Dooncito/fundamentos-de-dise-o/Imagenes/Caja_Negra.png

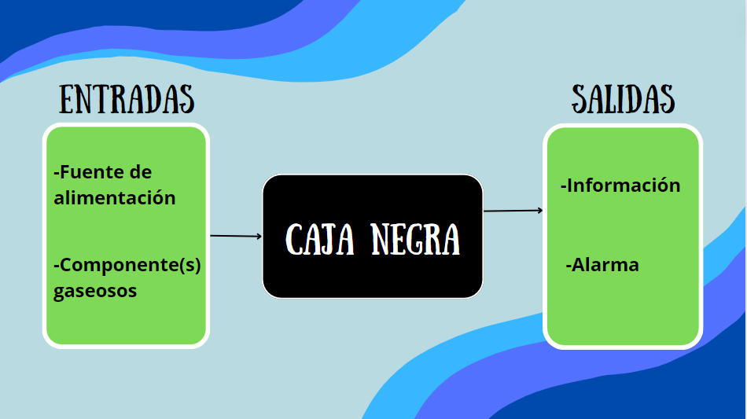
Imagenes/Caja_Negra.png
