Dooncito/fundamentos-de-dise-o/Imagenes/Esquema_de_Funciones.png

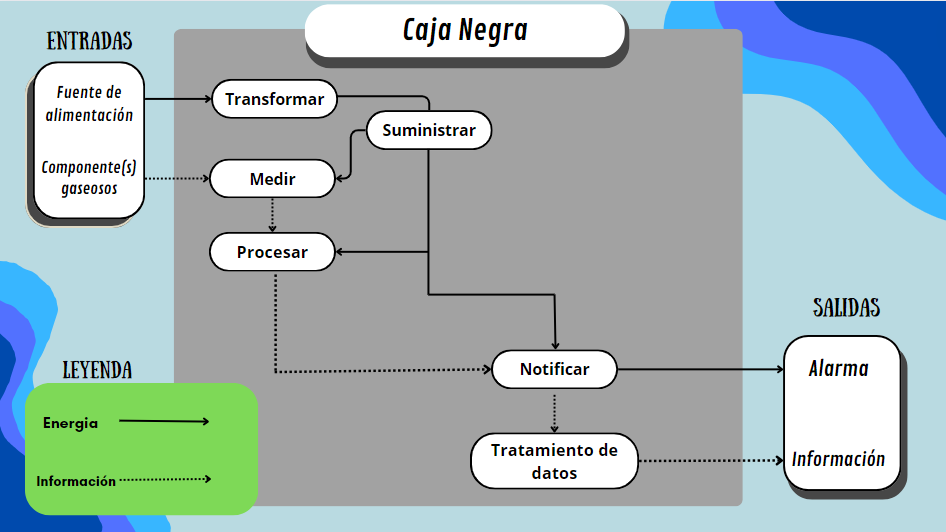
Imagenes/Esquema_de_Funciones.png
