Dooncito/fundamentos-de-dise-o/Imagenes/Funcionales.jpg

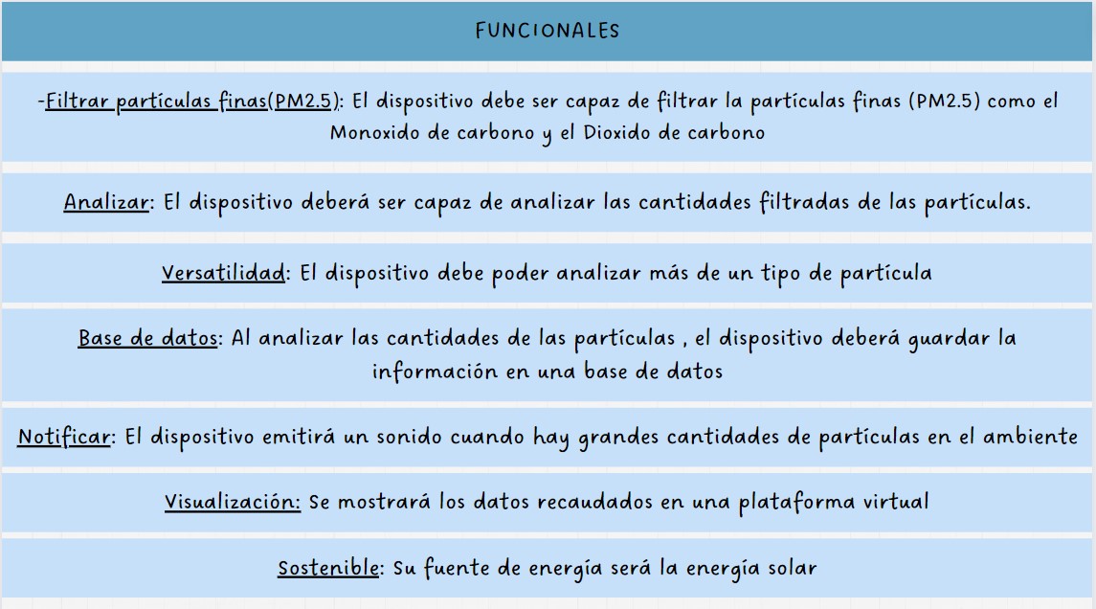
Imagenes/Funcionales.jpg
