Dooncito/fundamentos-de-dise-o/Imagenes/img entregable2/imgPro.jpg

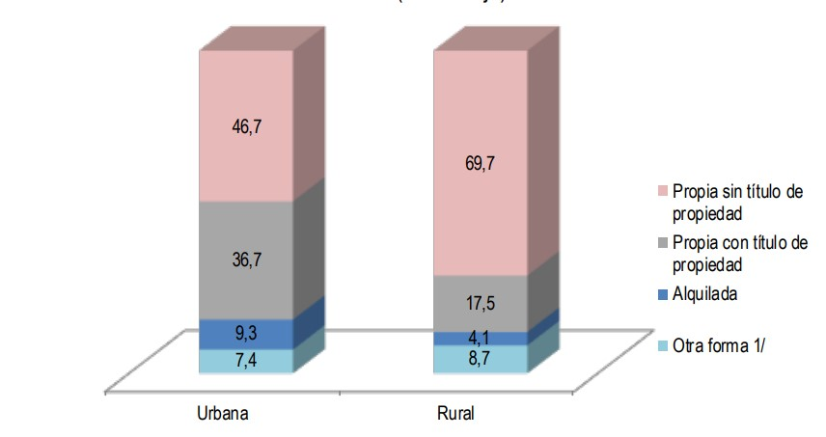
Imagenes/img entregable2/imgPro.jpg
