Dooncito/fundamentos-de-dise-o/Imagenes/img entregable2/Mapa de viaje.jpg

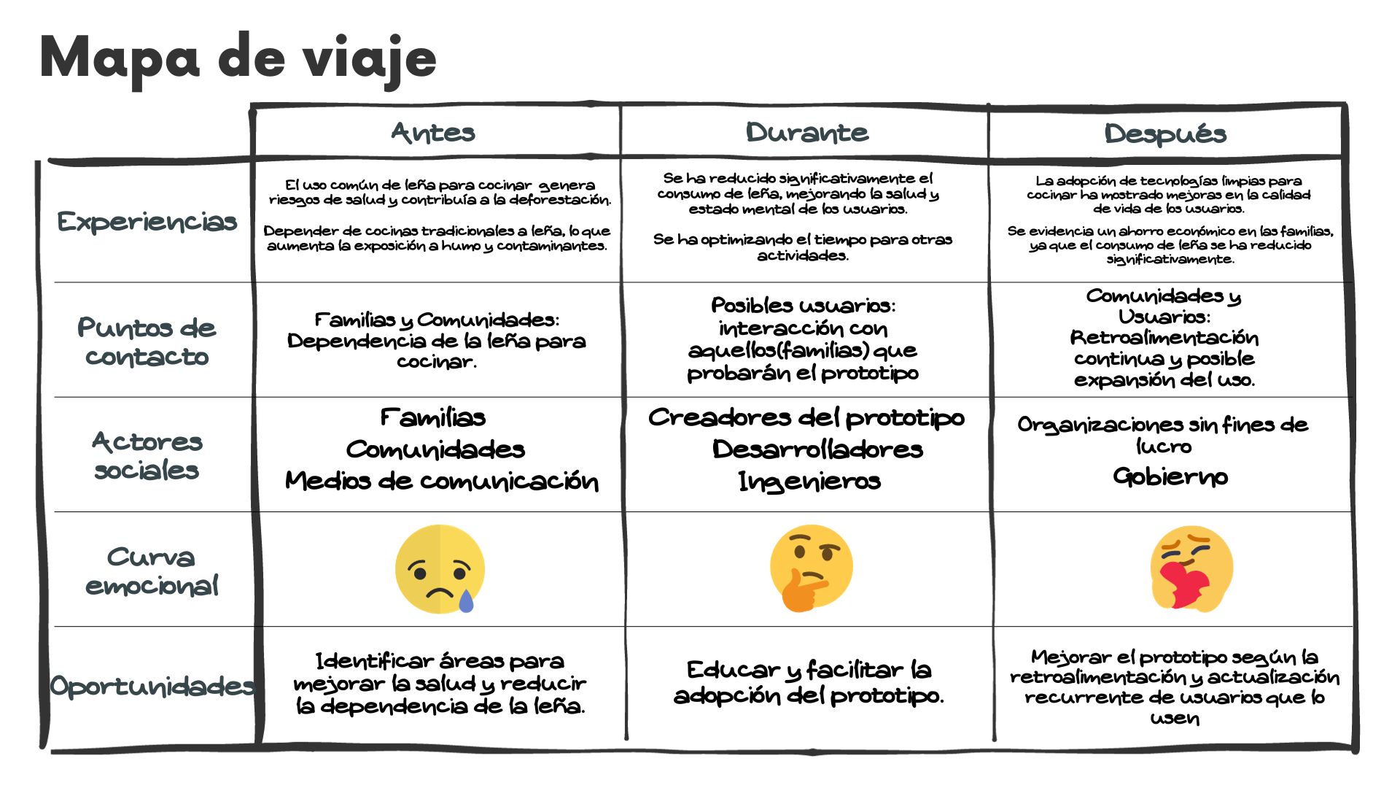
Imagenes/img entregable2/Mapa de viaje.jpg
