Dooncito/fundamentos-de-dise-o/Imagenes/img entregable2/Mapa empatía.jpg

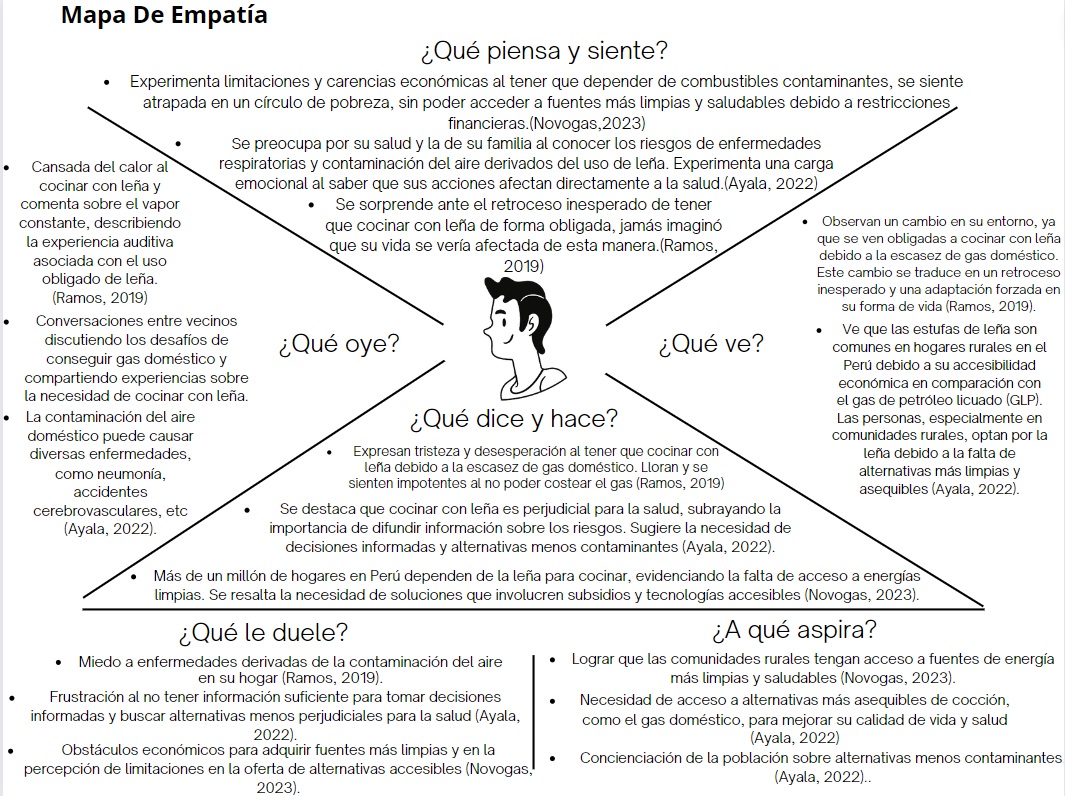
Imagenes/img entregable2/Mapa empatía.jpg
