Dooncito/fundamentos-de-dise-o/Imagenes/Img Monitoreo del aire.png

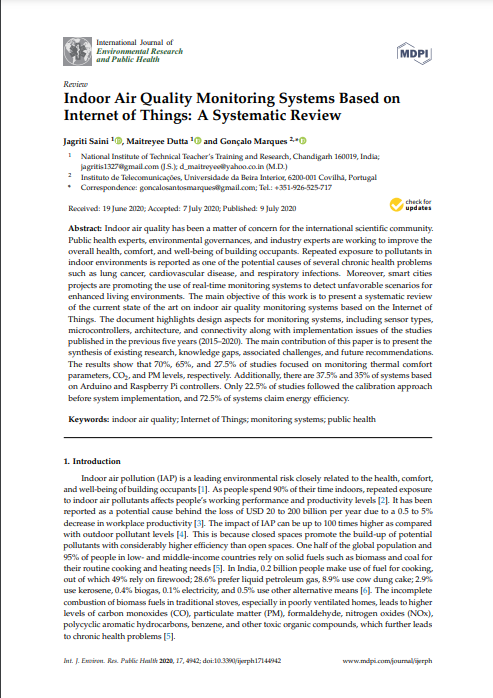
Imagenes/Img Monitoreo del aire.png
