Dooncito/fundamentos-de-dise-o/Imagenes/img_comercial_y_cienti/img anlásis de pm.jpeg

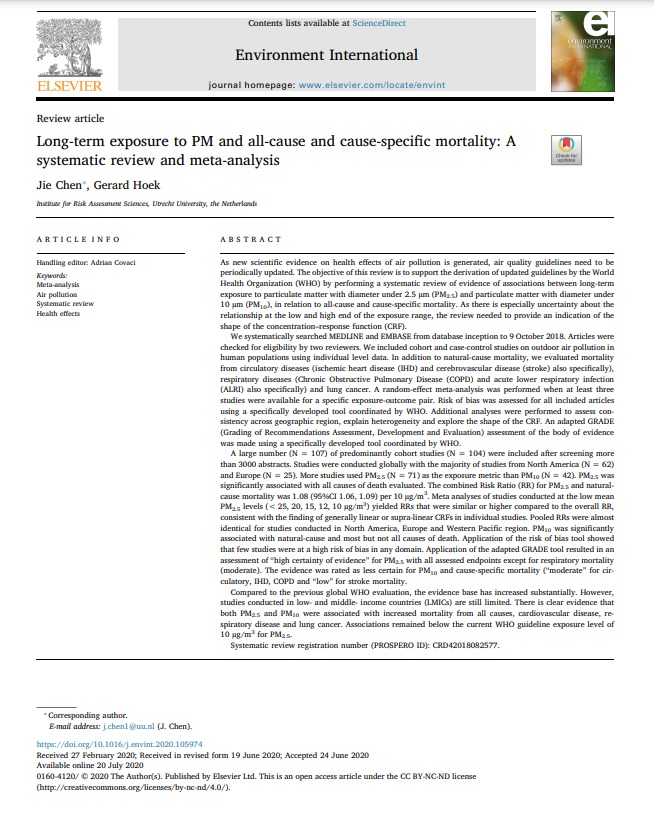
Imagenes/img_comercial_y_cienti/img anlásis de pm.jpeg
