Dooncito/fundamentos-de-dise-o/Imagenes/img_comercial_y_cienti/product2.jpg

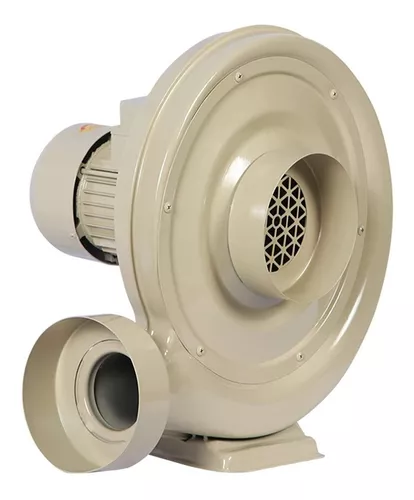
Imagenes/img_comercial_y_cienti/product2.jpg
