Dooncito/fundamentos-de-dise-o/Imagenes/img_entregable7/interior.png

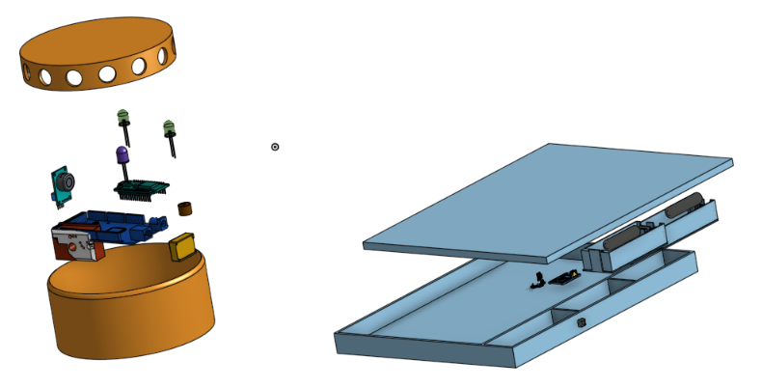
Imagenes/img_entregable7/interior.png
