Dooncito/fundamentos-de-dise-o/Imagenes/img_entregable7/planocargador.png

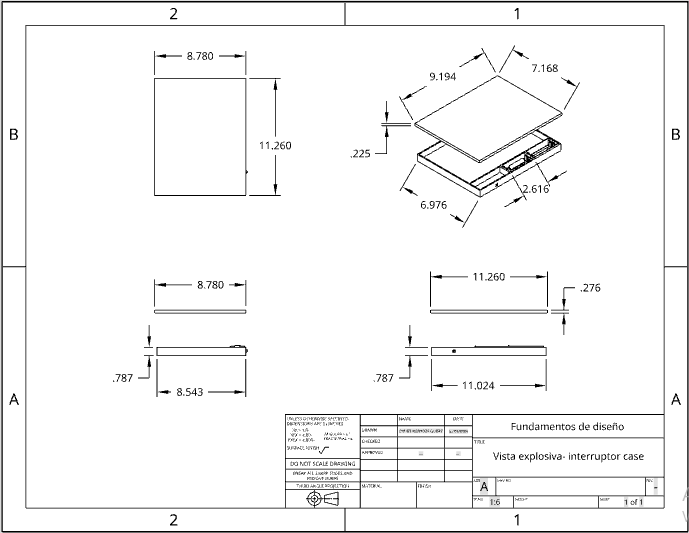
Imagenes/img_entregable7/planocargador.png
