Dooncito/fundamentos-de-dise-o/Imagenes/img_entregable7/planodela_alarma.png

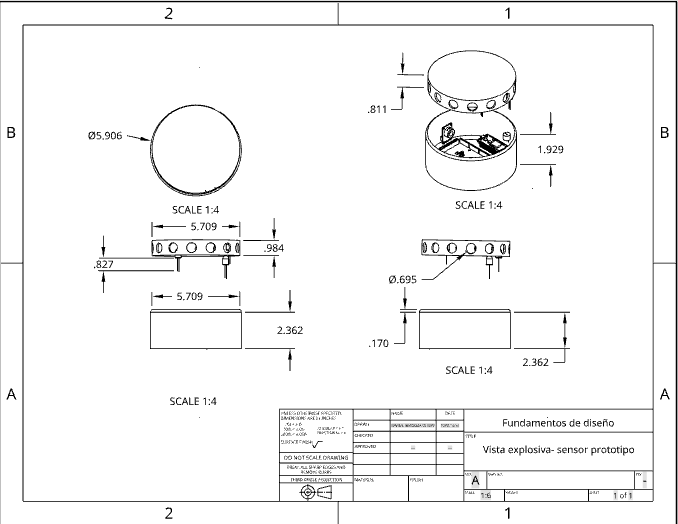
Imagenes/img_entregable7/planodela_alarma.png
