Dooncito/fundamentos-de-dise-o/Imagenes/img_hito1/tecnico.png

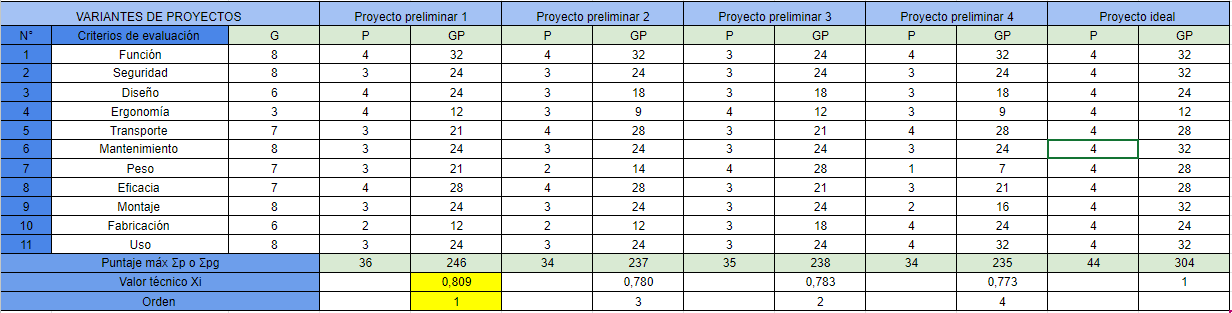
Imagenes/img_hito1/tecnico.png
