Dooncito/fundamentos-de-dise-o/Imagenes/lab2/Imagen de WhatsApp 2024-01-22 a las 20.52.30_695c96ab.jpg

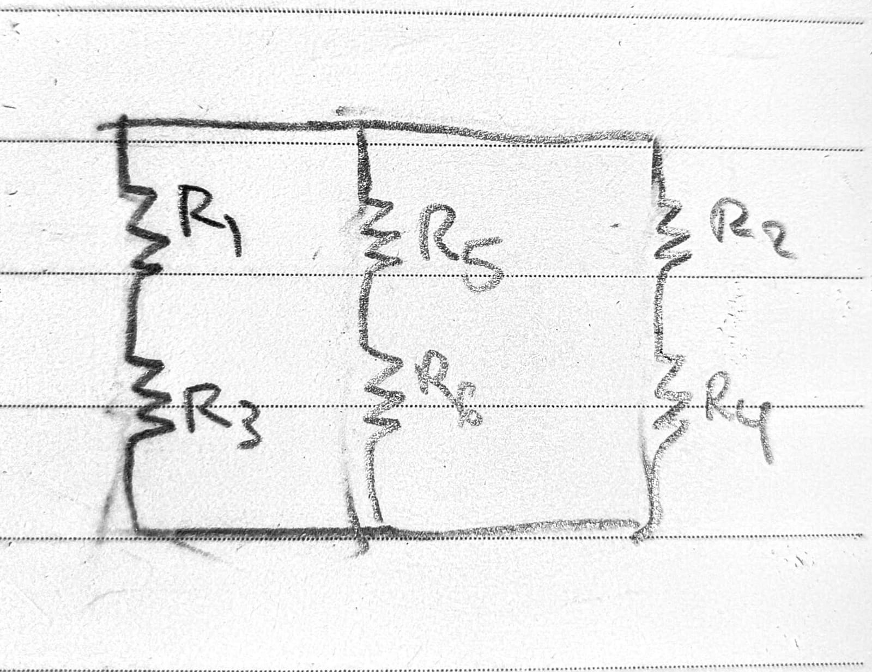
Imagenes/lab2/Imagen de WhatsApp 2024-01-22 a las 20.52.30_695c96ab.jpg
