Dooncito/fundamentos-de-dise-o/Imagenes/T.R. Funsionales.jpeg

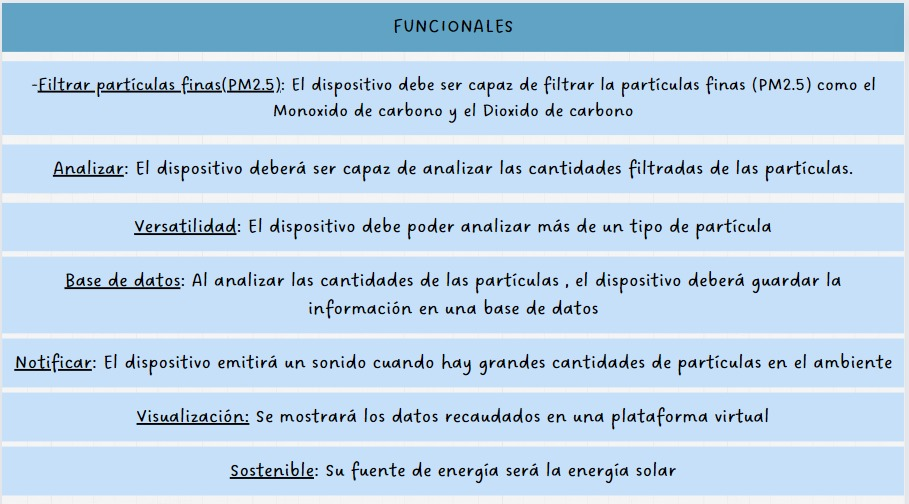
Imagenes/T.R. Funsionales.jpeg
